frieger/atsam3s2ba-devboard/tuner_mcu.sch

## KiCad design tuner_mcu.sch (2012-08-06)

Schematic: tuner_mcu.sch

Parts:
C1, C7, C10, C18, C19, C20: 2.2uF
C2, C17: 10uF
C3, C4, C5, C6, C8, C9, C11, C21, C22: 100nF
C12: 100uF
C13, C14, C15, C16: as needed
D1, D2: LED
HOLE1, HOLE2: SCREWHOLE_FR
HS1: HEATSINK
IC1: ATSAM3S2BA
IC2: TCN75A
J1: MINI-USB
JP1, JP2, JP3, JP4: JUMPER
P1, P2, P3, P4, P5, P6, P7, P8, P9, P10, P12, P13: CONN_4
P11, P14: CONN_2
R1, R2, R3, R4: R
R5, R6: 4.7k
SW1: erase-switch
SW2: reset-switch
SW3, SW4: SWITCH
U1: MCP1703-3.3
X1: WATCH-CRYSTAL
X2: 16MHz
fid1, fid2: CONN_1

Notes on the sheet:
see documentation for capacitor values
Recommended: Panasonic EEUFR1C101H
Temperature sensor
ATSAM3S2BA development board Felix Rieger, 2012-08-05
flash erase
10uF tantalum 100uF electrolytic
jumpers for usb power
jumpers for usb data
user led
power led
pin header to connect signals if no crystal is used
